micropolimi/MAPPI/images/post_holder_5cm.jpeg

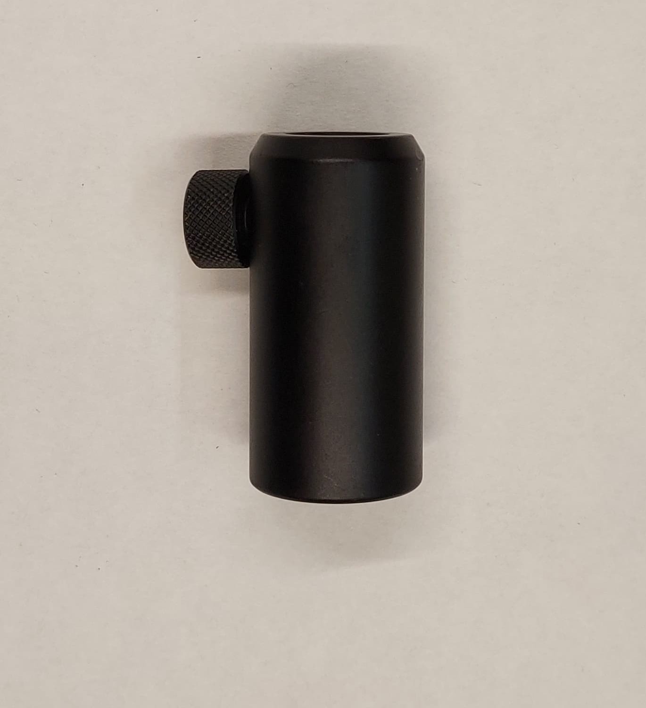
images/post_holder_5cm.jpeg
