micropolimi/MAPPI/images/unknown.jpeg

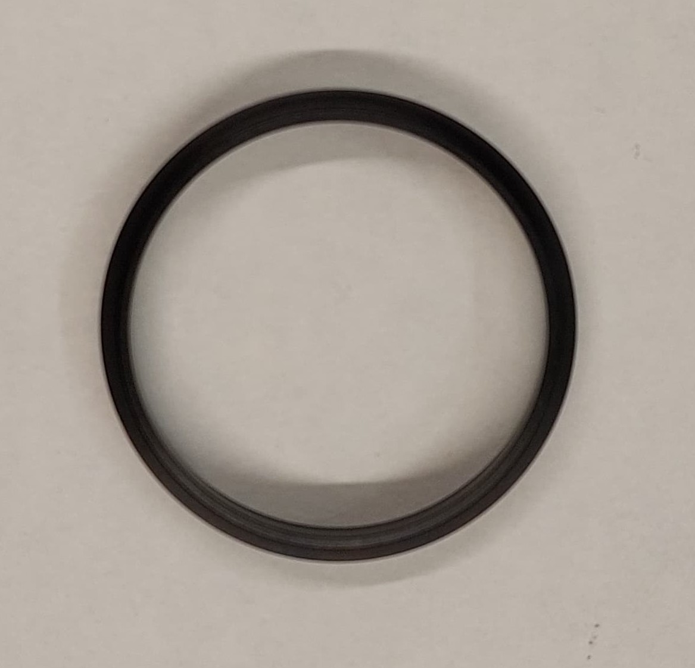
images/unknown.jpeg
