micropolimi/MAPPI/src/MAPPI_System/Settings/backup.ini

[app]
save_dir = C:\data\temp
sample = 
data_fname_format = {timestamp:%y%m%d_%H%M%S}_{measurement.name}.{ext}

[hardware/camera_y]
connected = True
debug_mode = False
name = Point Grey Research 14103019 Grasshopper3 GS3-U3-23S6M
number = 0
image_width = 1920
image_height = 1200
frame_rate = 1.0
exposure_time = 799.9379634857178
frame_num = 2
acquisition_mode = Continuous
gain = 0.0
temperature = 52.55000000000001

[hardware/camera_x]
connected = True
debug_mode = False
name = Point Grey Research 17289280 Grasshopper3 GS3-U3-23S6M
number = 1
image_width = 1920
image_height = 1200
frame_rate = 1.0
exposure_time = 799.9379634857178
frame_num = 2
acquisition_mode = Continuous
gain = 0.0
temperature = 52.85000000000002

[hardware/led_y]
connected = True
debug_mode = False
port = COM3
channel 1 = False

[hardware/led_x]
connected = True
debug_mode = False
port = COM4
channel 1 = False

[measurement/PlantTimeLapseDualMeasure]
activation = False
run_state = stop_interrupted
progress = 0.0
profile = False
camera_in_use = X
acquisition_time = 799.9379634857178
time_lapse_num = 10
time_lapse_waiting_time = 2.0
frame_num = 1
LED_init_time = 0.0
xsampling = 0.0586
ysampling = 0.0586
zsampling = 1.0
auto_range = True
auto_levels = True
level_min = 22016
level_max = 65408
save_h5 = False
refresh_period = 0.05
